Narensraj/pcb_designing/ESP32_RelayBoard/3D_PCB_ESP32_RelayControl_3.png

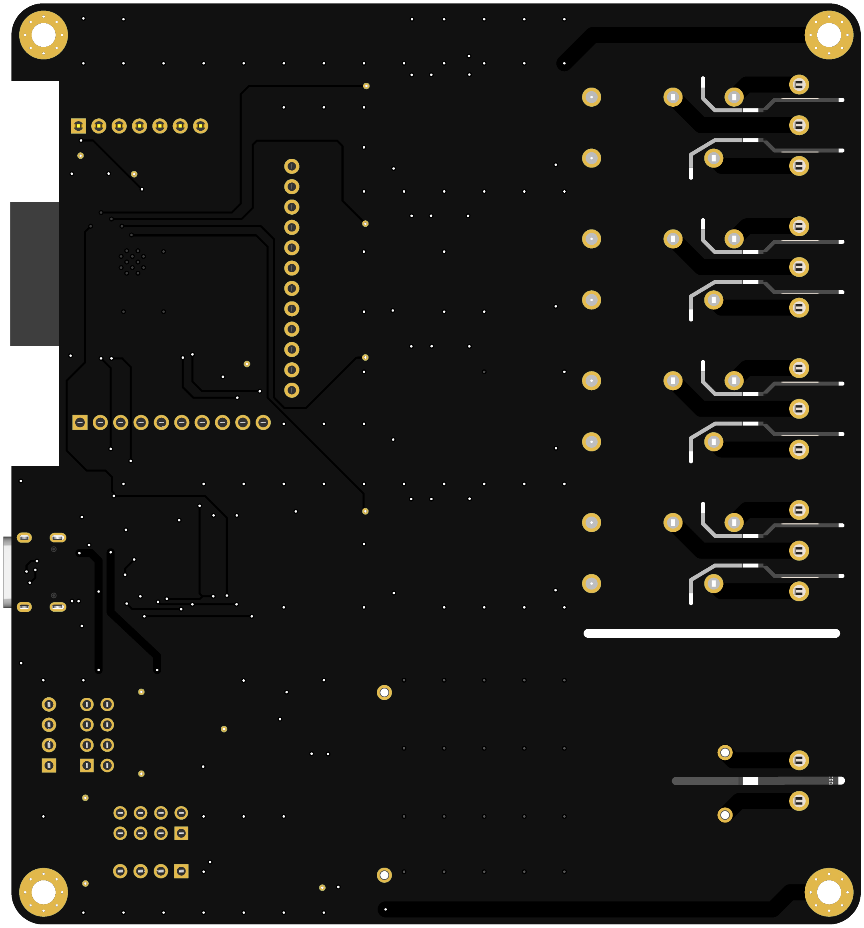
ESP32_RelayBoard/3D_PCB_ESP32_RelayControl_3.png
