Narensraj/pcb_designing/Project_G/Board Images/2.jpg

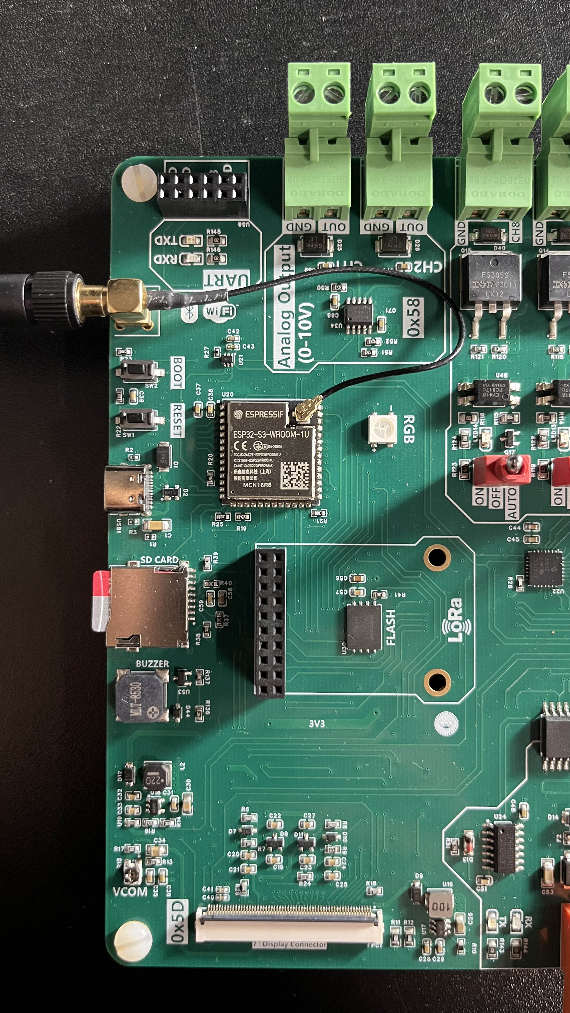
Project_G/Board Images/2.jpg
