Narensraj/pcb_designing/Project_G/Board Images/3.jpg

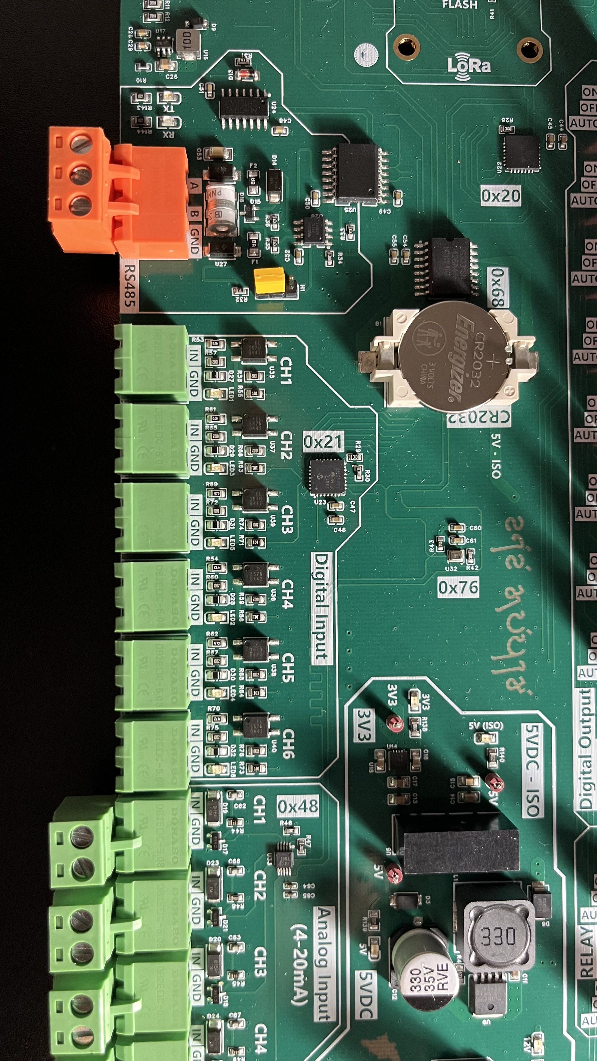
Project_G/Board Images/3.jpg
