Narensraj/pcb_designing/Project_G/Board Images/4.jpg

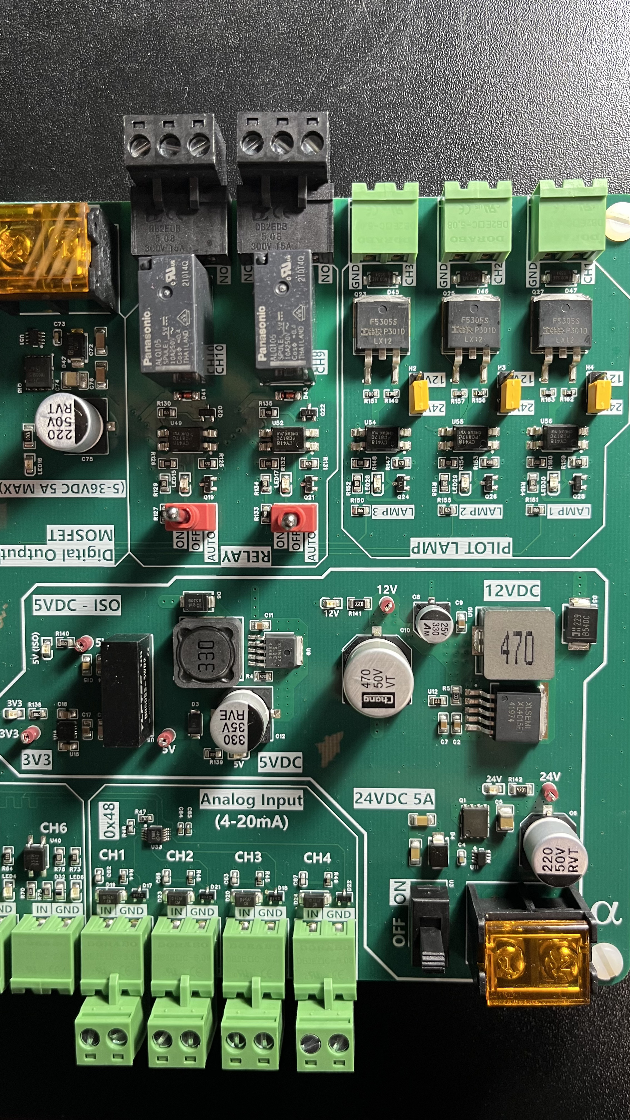
Project_G/Board Images/4.jpg
