Narensraj/pcb_designing/Project_G/Board Images/5.jpg

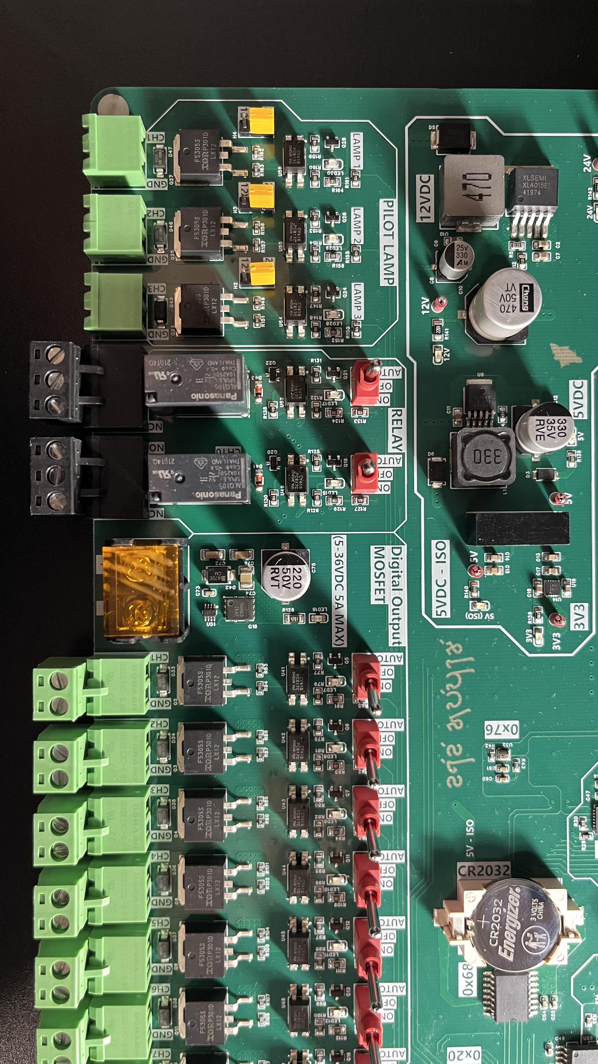
Project_G/Board Images/5.jpg
