Narensraj/pcb_designing/Project_G/Board Images/6.jpg

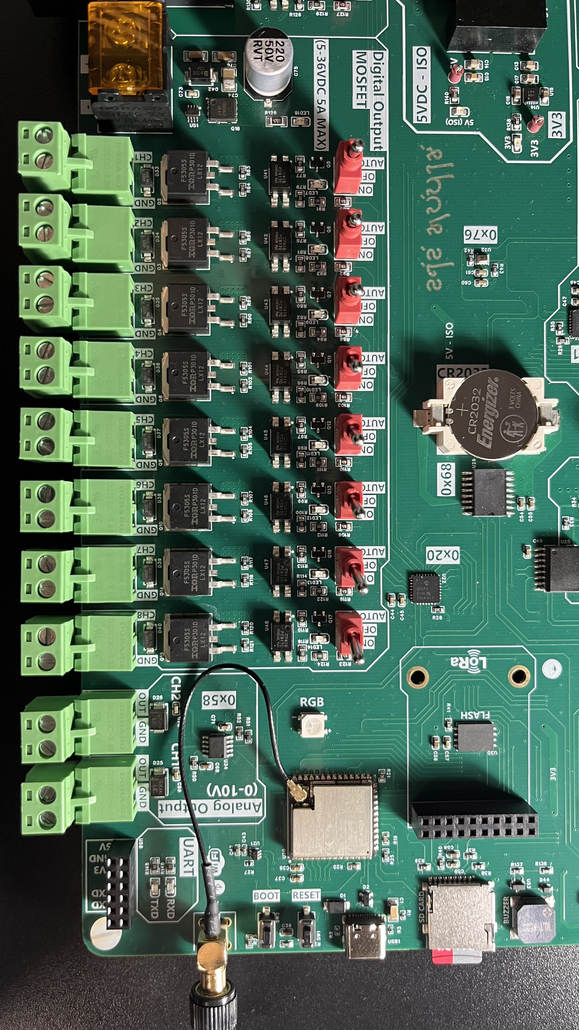
Project_G/Board Images/6.jpg
