Narensraj/pcb_designing/Project_G/Board Images/7.jpg

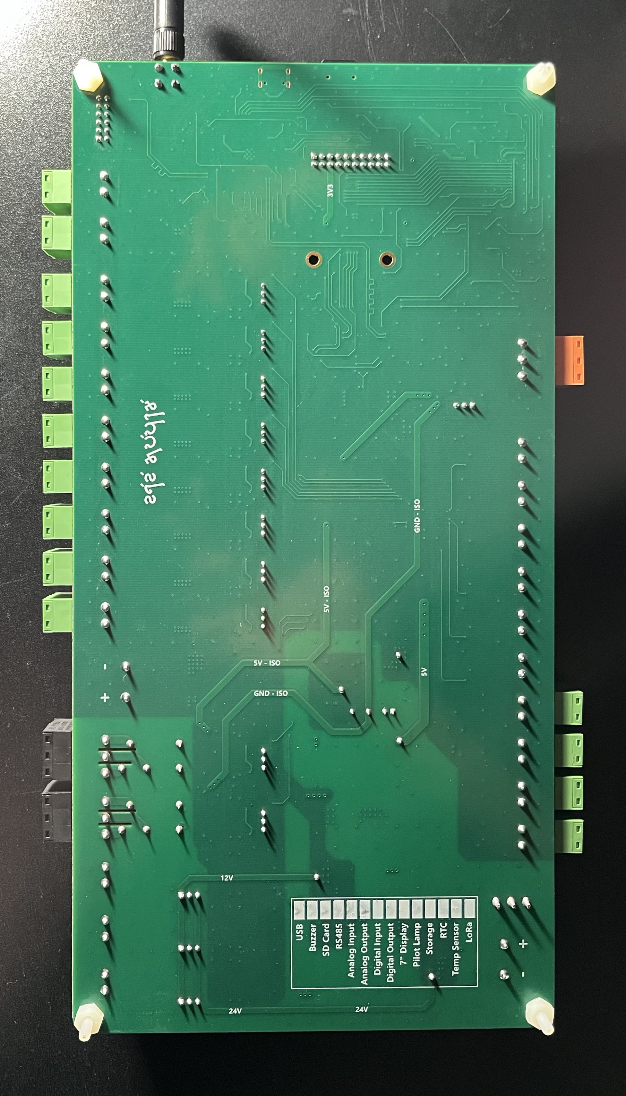
Project_G/Board Images/7.jpg
