Narensraj/pcb_designing/Project_G/CAD Images/1.png

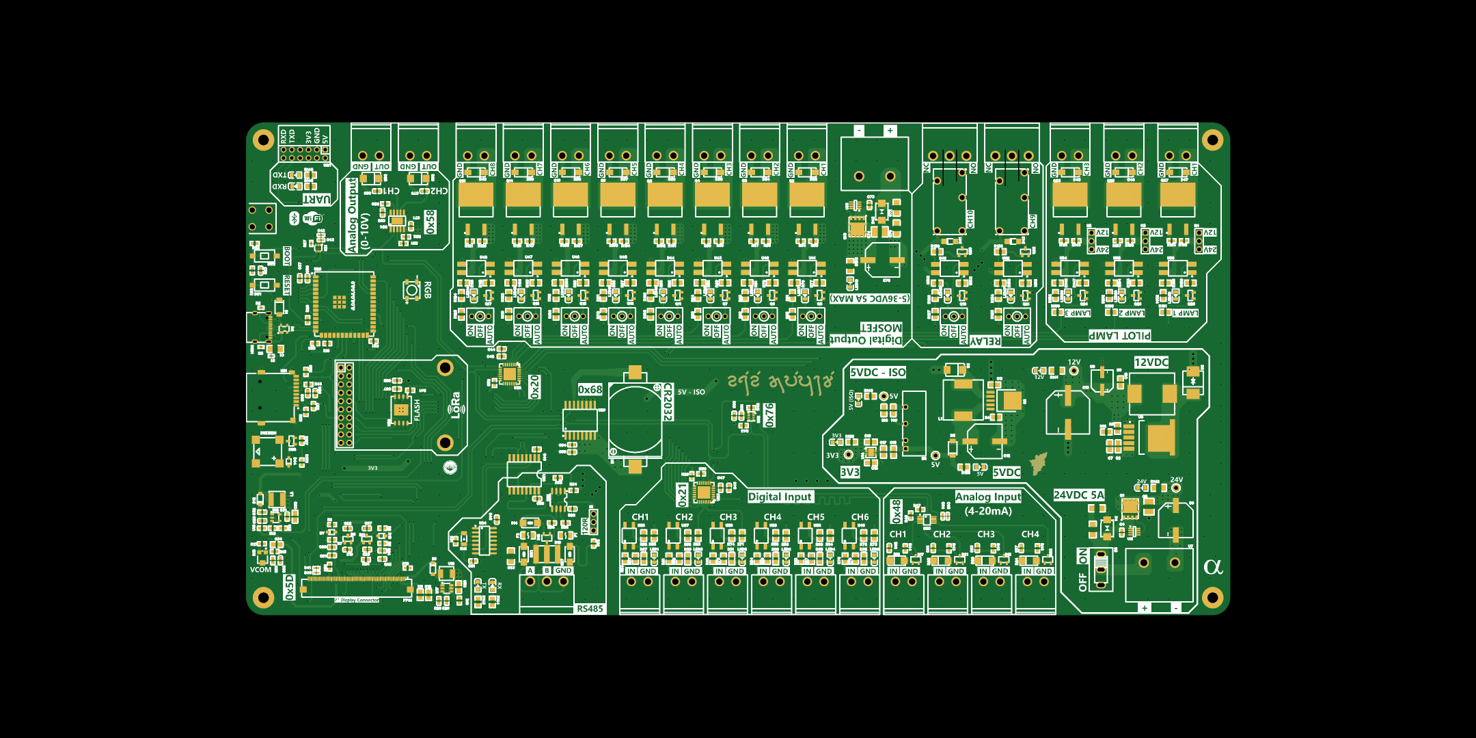
Project_G/CAD Images/1.png
