Narensraj/pcb_designing/Project_G/CAD Images/2.png

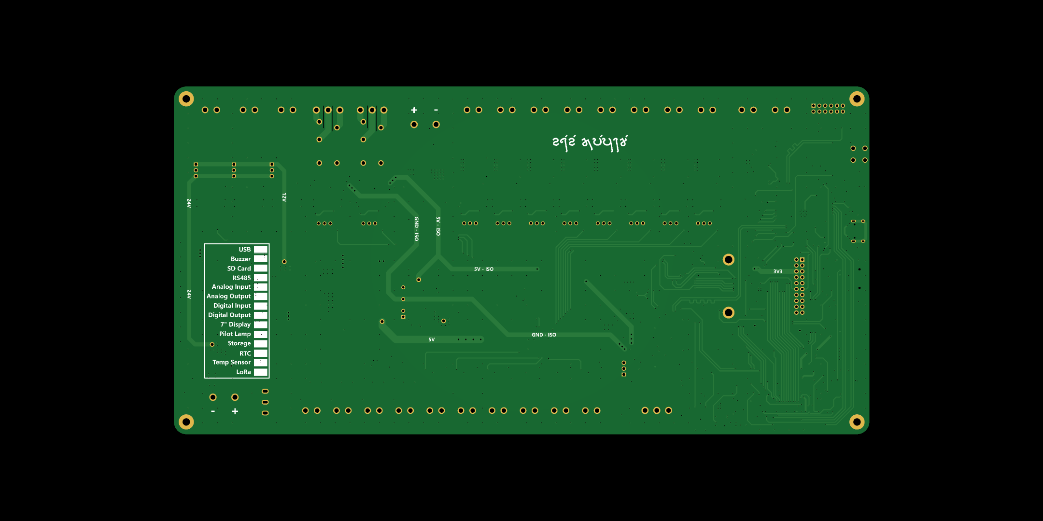
Project_G/CAD Images/2.png
