Narensraj/pcb_designing/Project_G/CAD Images/3.png

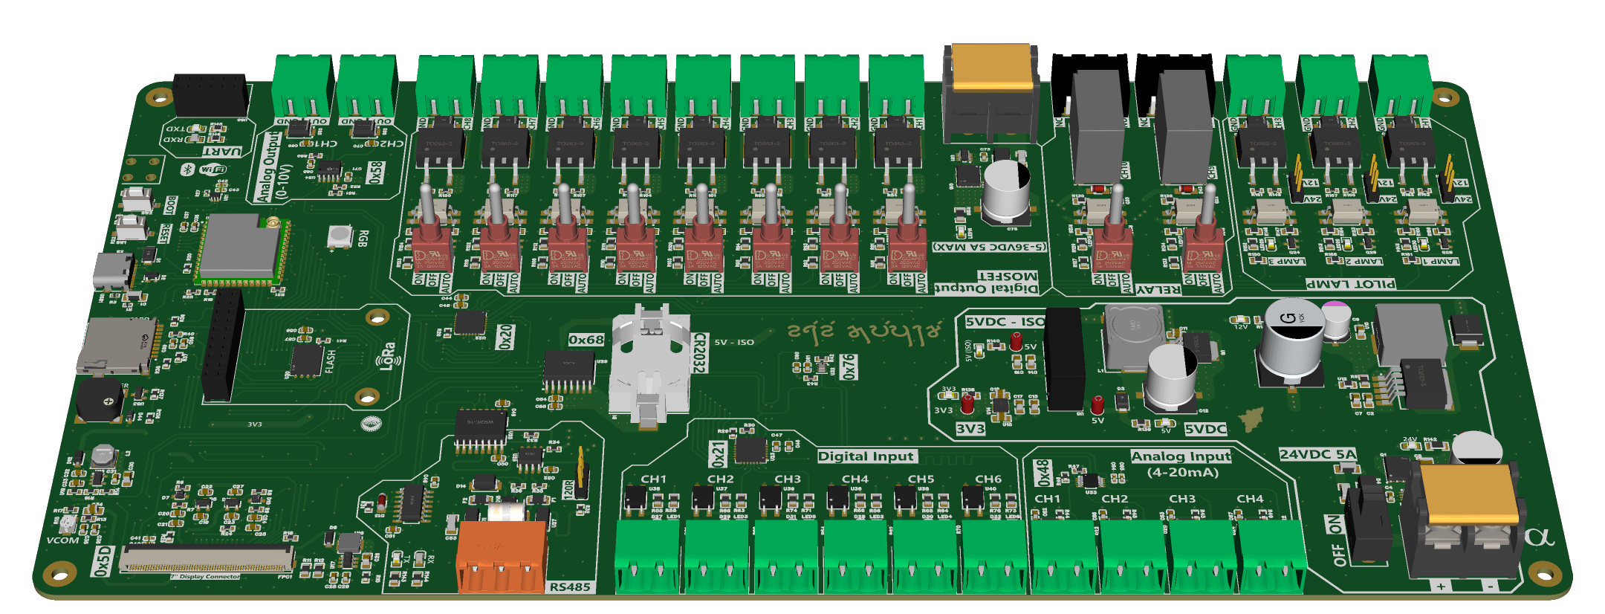
Project_G/CAD Images/3.png
