Narensraj/pcb_designing/Project_G/CAD Images/4.png

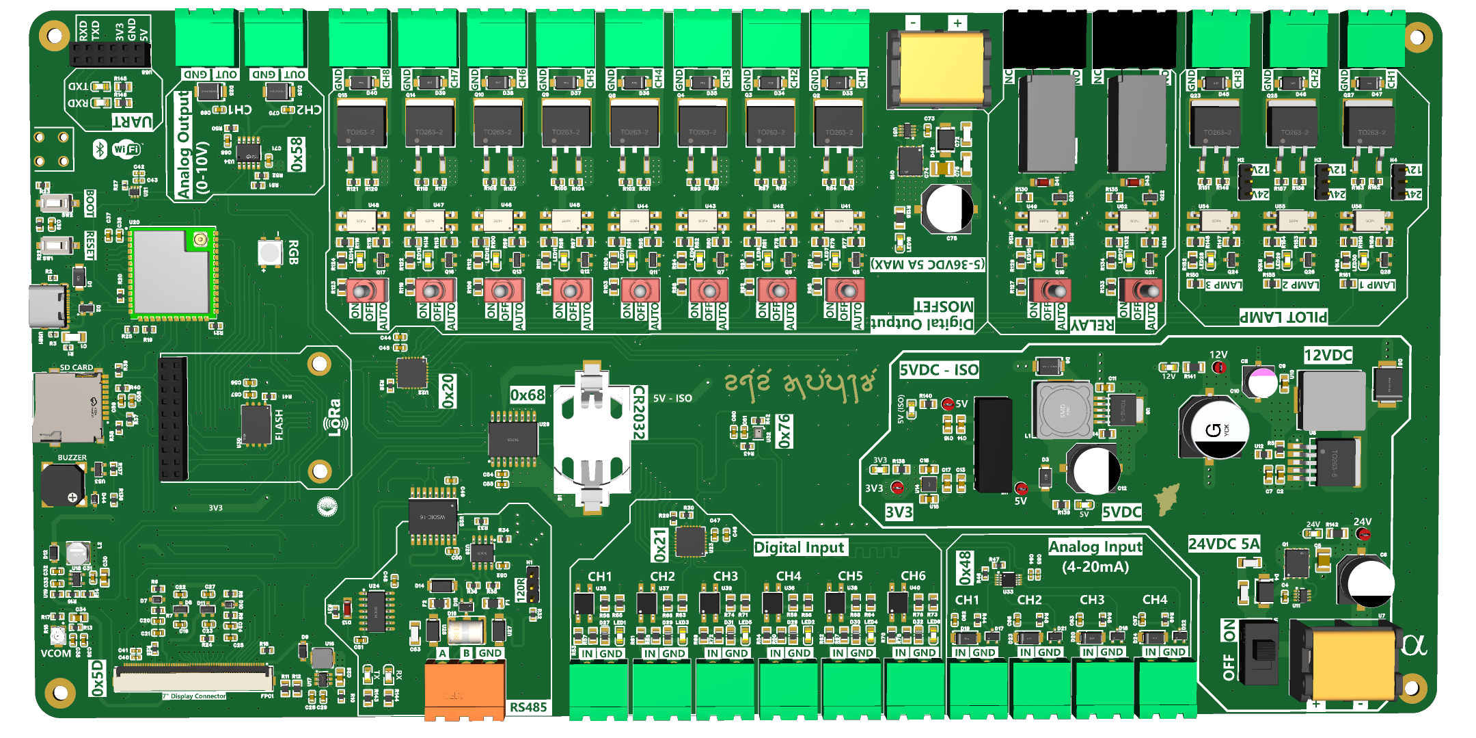
Project_G/CAD Images/4.png
