Narensraj/pcb_designing/Project_G/CAD Images/5.png

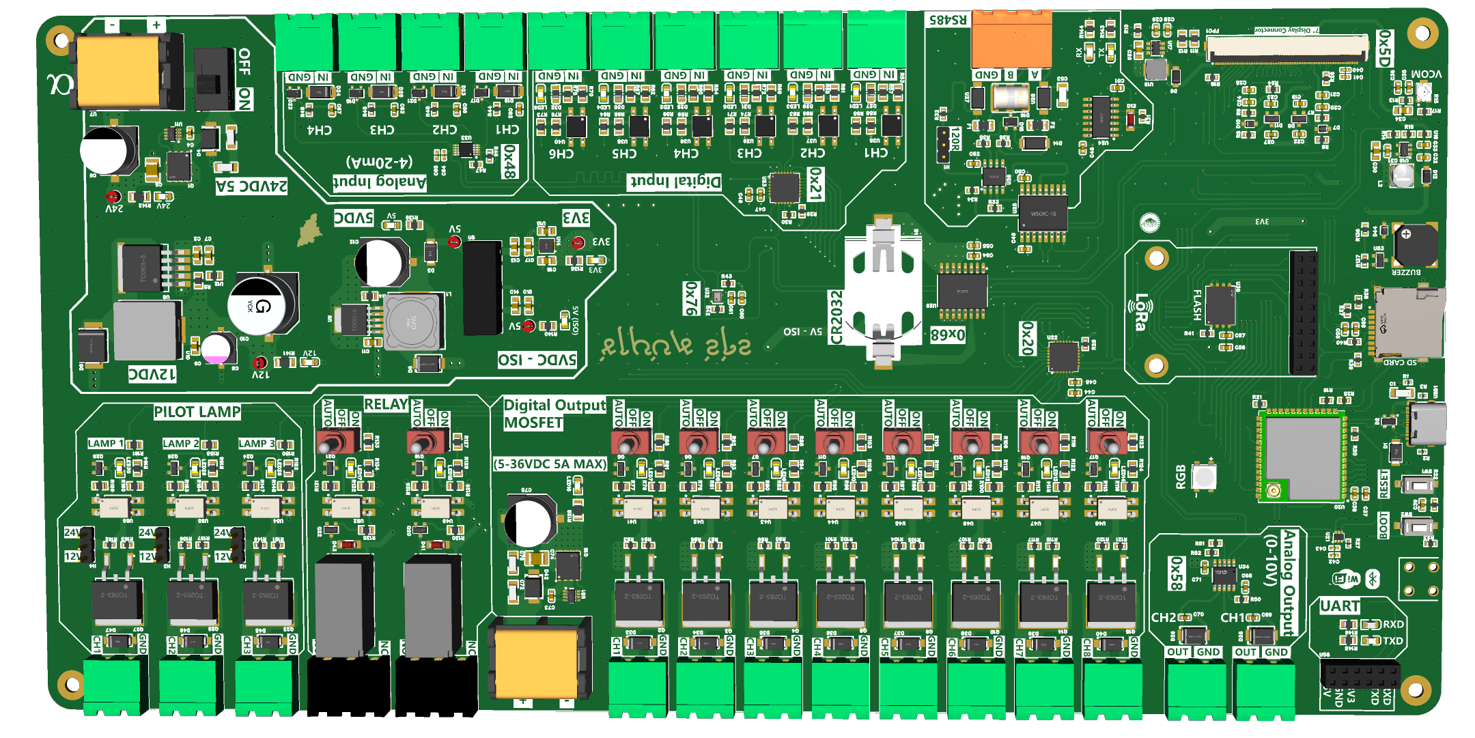
Project_G/CAD Images/5.png
