Narensraj/pcb_designing/Project_G/CAD Images/6.png

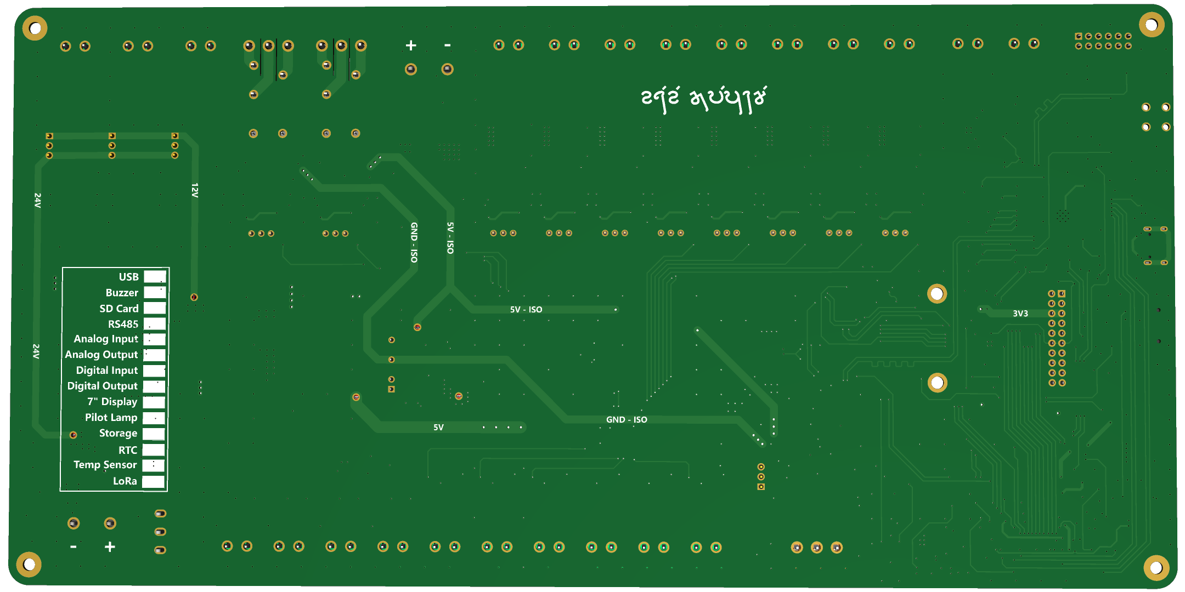
Project_G/CAD Images/6.png
