Narensraj/pcb_designing/Project_G/Documents/PCB Layer Images/Bottom_Layer.jpg

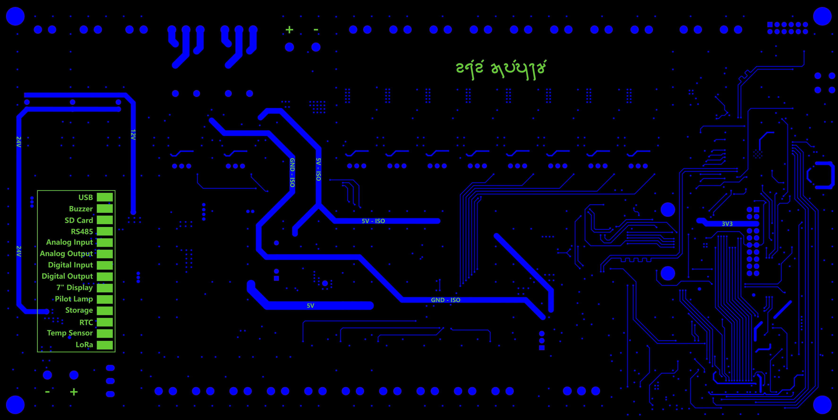
Project_G/Documents/PCB Layer Images/Bottom_Layer.jpg
