Narensraj/pcb_designing/Project_G/Documents/PCB Layer Images/Ground_Layer.jpg

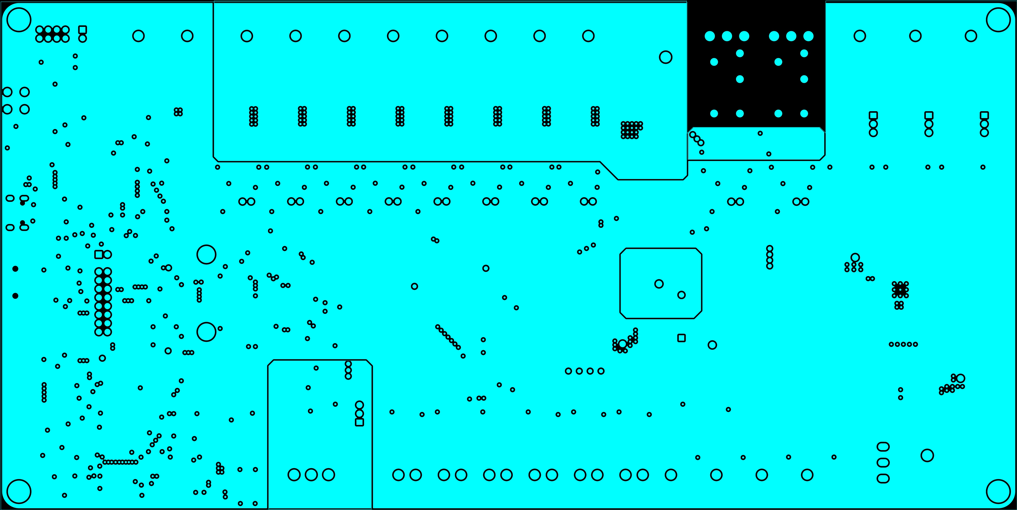
Project_G/Documents/PCB Layer Images/Ground_Layer.jpg
