Narensraj/pcb_designing/Project_G/Documents/PCB Layer Images/Power_Layer.jpg

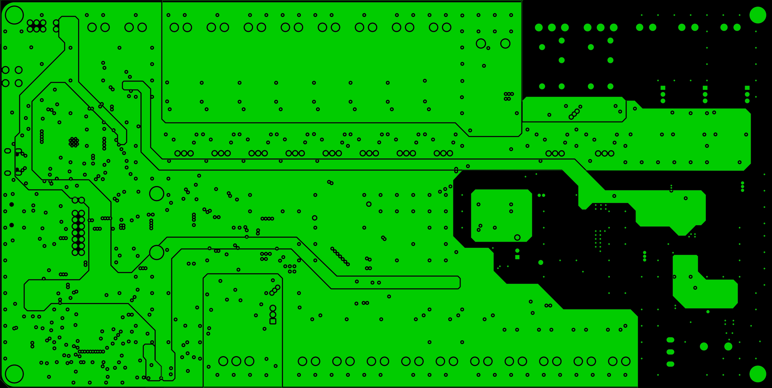
Project_G/Documents/PCB Layer Images/Power_Layer.jpg
