Narensraj/pcb_designing/Project_G/Documents/PCB Layer Images/Top_Layer.jpg

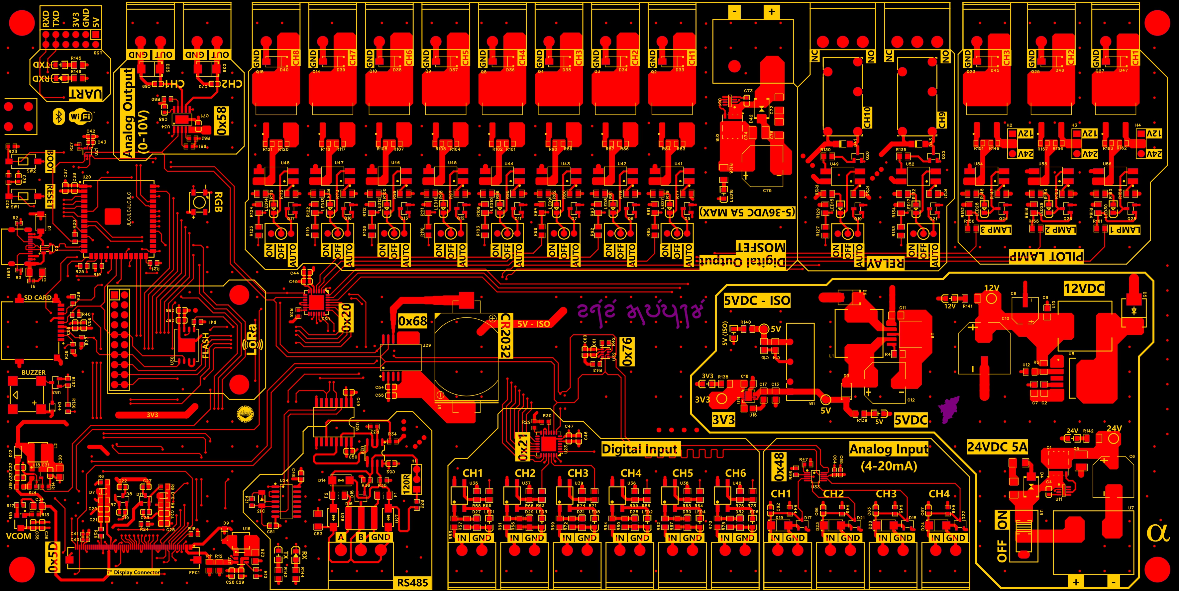
Project_G/Documents/PCB Layer Images/Top_Layer.jpg
