Narensraj/pcb_designing/Project_G/Reference Manual and Datasheet/components_DS3231_QT_sch (RTC).png

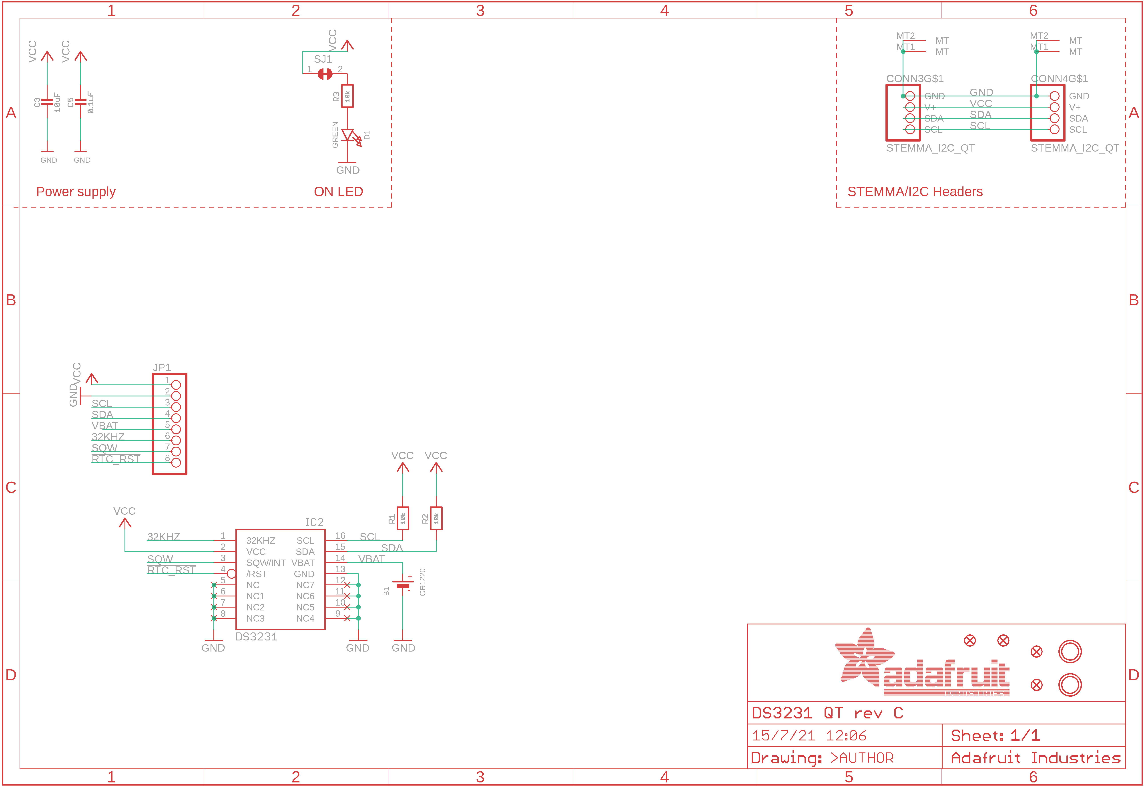
Project_G/Reference Manual and Datasheet/components_DS3231_QT_sch (RTC).png
