Narensraj/pcb_designing/Project_G/Reference Manual and Datasheet/adafruit_products_LTC4311_sch.png

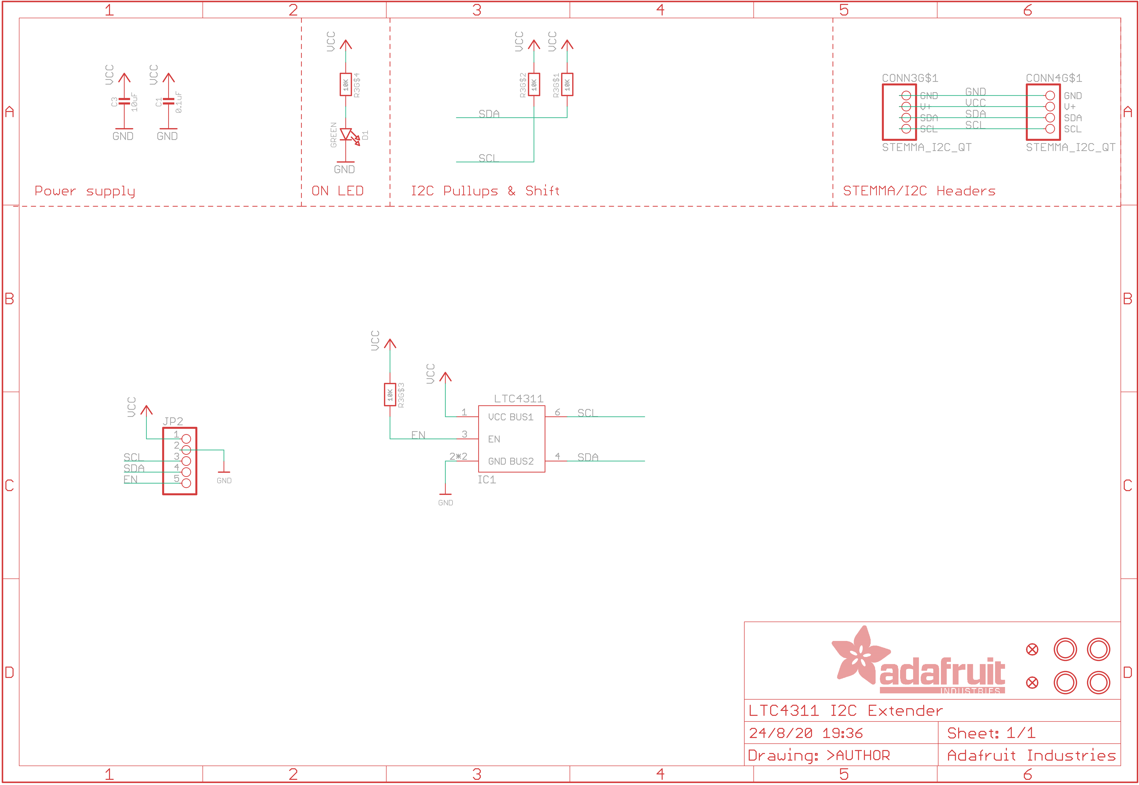
Project_G/Reference Manual and Datasheet/adafruit_products_LTC4311_sch.png
