Narensraj/pcb_designing/Project_G/Reference Manual and Datasheet/EB-101-0023_1.png

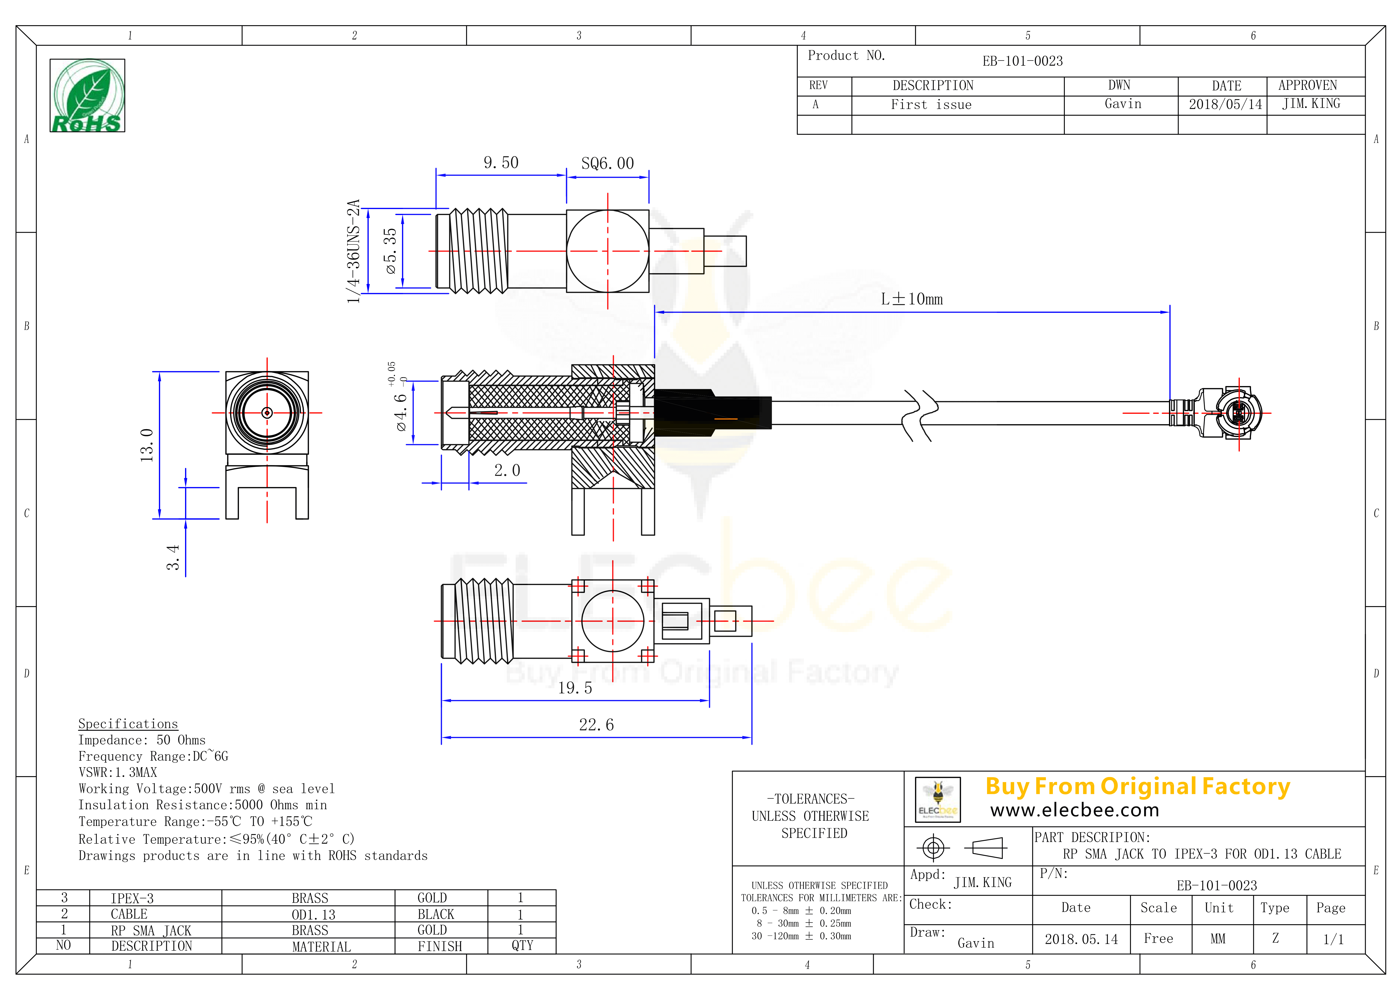
Project_G/Reference Manual and Datasheet/EB-101-0023_1.png
