Narensraj/pcb_designing/Project_G/Test codes and examples/Analog_Input/Output.png

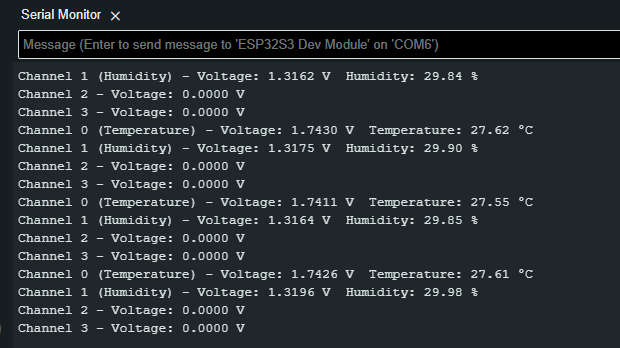
Project_G/Test codes and examples/Analog_Input/Output.png
