Narensraj/pcb_designing/Project_G/Test codes and examples/BMP280/Output.png

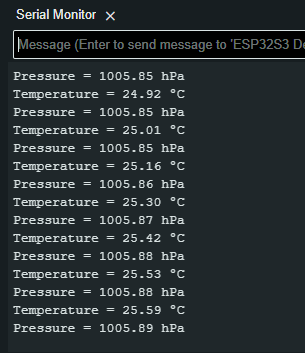
Project_G/Test codes and examples/BMP280/Output.png
