Narensraj/pcb_designing/Project_G/Test codes and examples/Digital_Outputs/Outputs.png

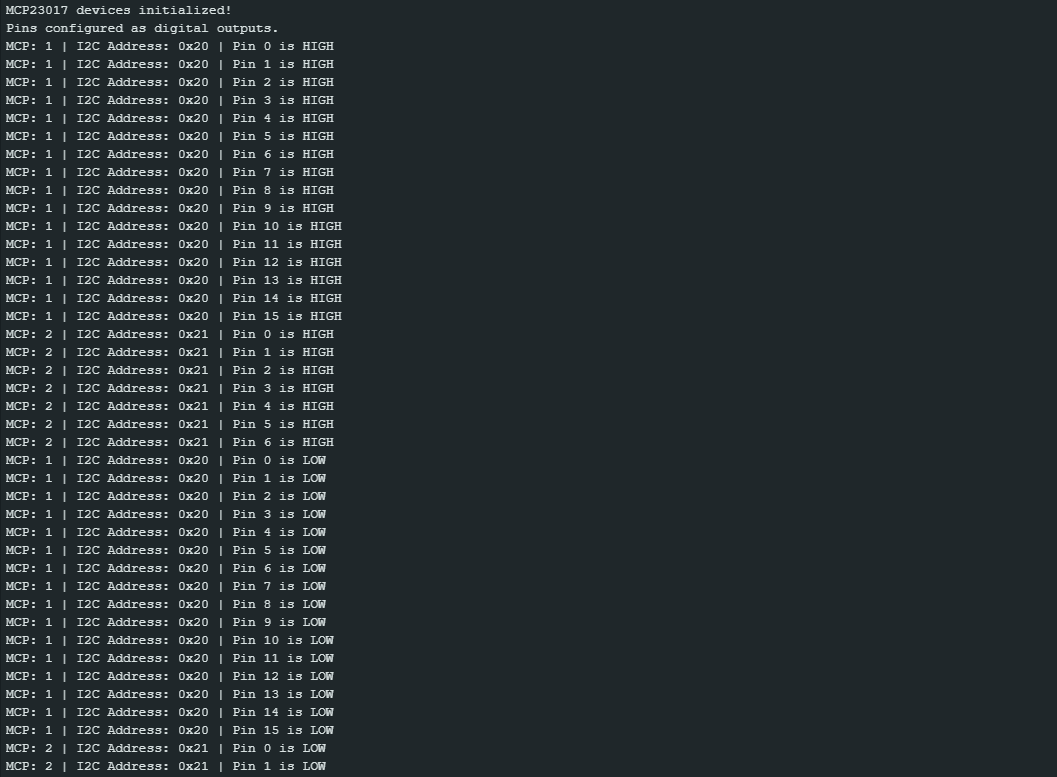
Project_G/Test codes and examples/Digital_Outputs/Outputs.png
