Narensraj/pcb_designing/Project_G/Test codes and examples/ESP32-S3 Board Configuration.png

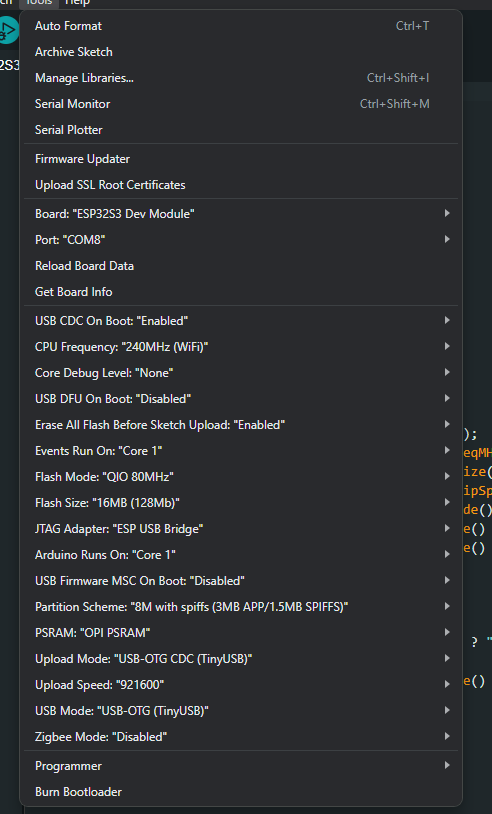
Project_G/Test codes and examples/ESP32-S3 Board Configuration.png
