Narensraj/pcb_designing/Project_G/Test codes and examples/I2C_Test/Output.png

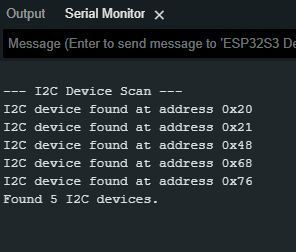
Project_G/Test codes and examples/I2C_Test/Output.png
