Narensraj/pcb_designing/Project_G/Test codes and examples/Modbus_Test/Output.png

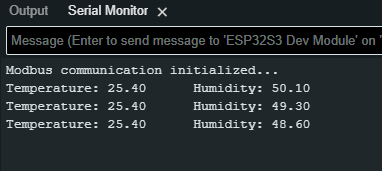
Project_G/Test codes and examples/Modbus_Test/Output.png
