Narensraj/pcb_designing/Project_G/Test codes and examples/RGB/Output.gif

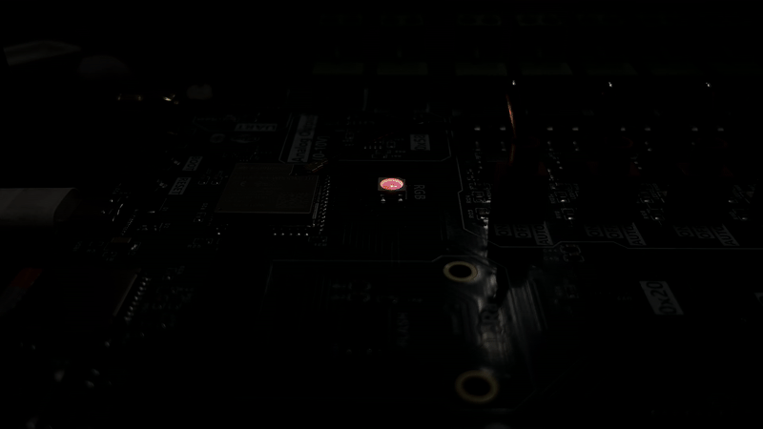
Project_G/Test codes and examples/RGB/Output.gif
