Narensraj/pcb_designing/Project_G/Test codes and examples/RTC/Output.png

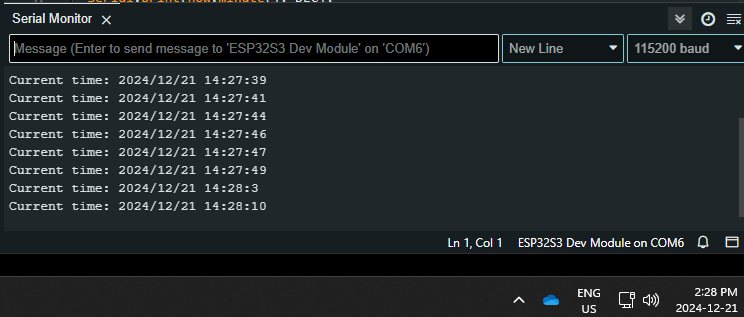
Project_G/Test codes and examples/RTC/Output.png
