Narensraj/pcb_designing/Project_G/Test codes and examples/SDCard_Test/Output.png

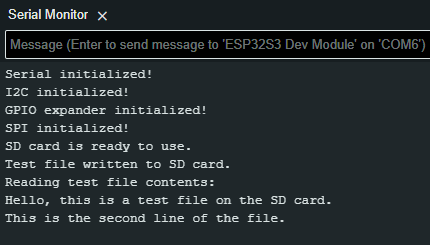
Project_G/Test codes and examples/SDCard_Test/Output.png
