Narensraj/pcb_designing/Project_G/Board Images/1.jpg

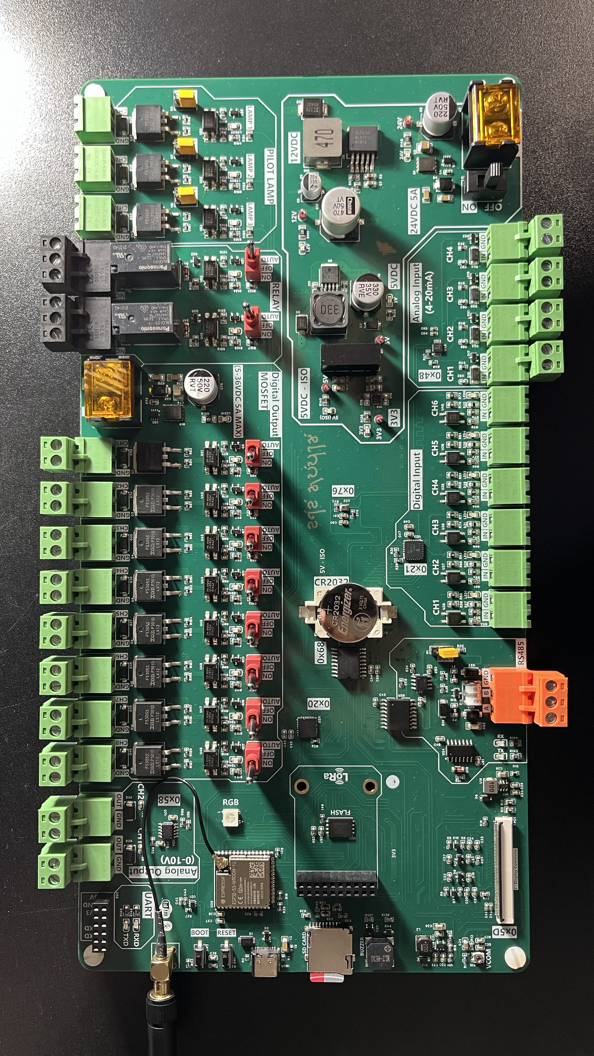
Project_G/Board Images/1.jpg
